aditocco2/overblinking/media/huell.gif

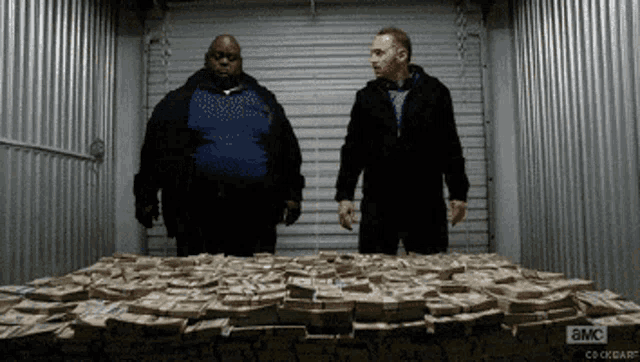
media/huell.gif
