aditocco2/overblinking/media/patriot.jpg

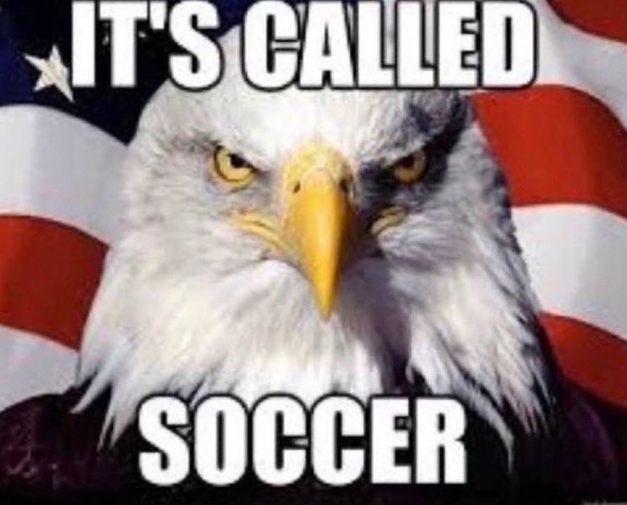
media/patriot.jpg
