aditocco2/overblinking/FreeRTOS-Kernel-main/.github/media/pr_process.png

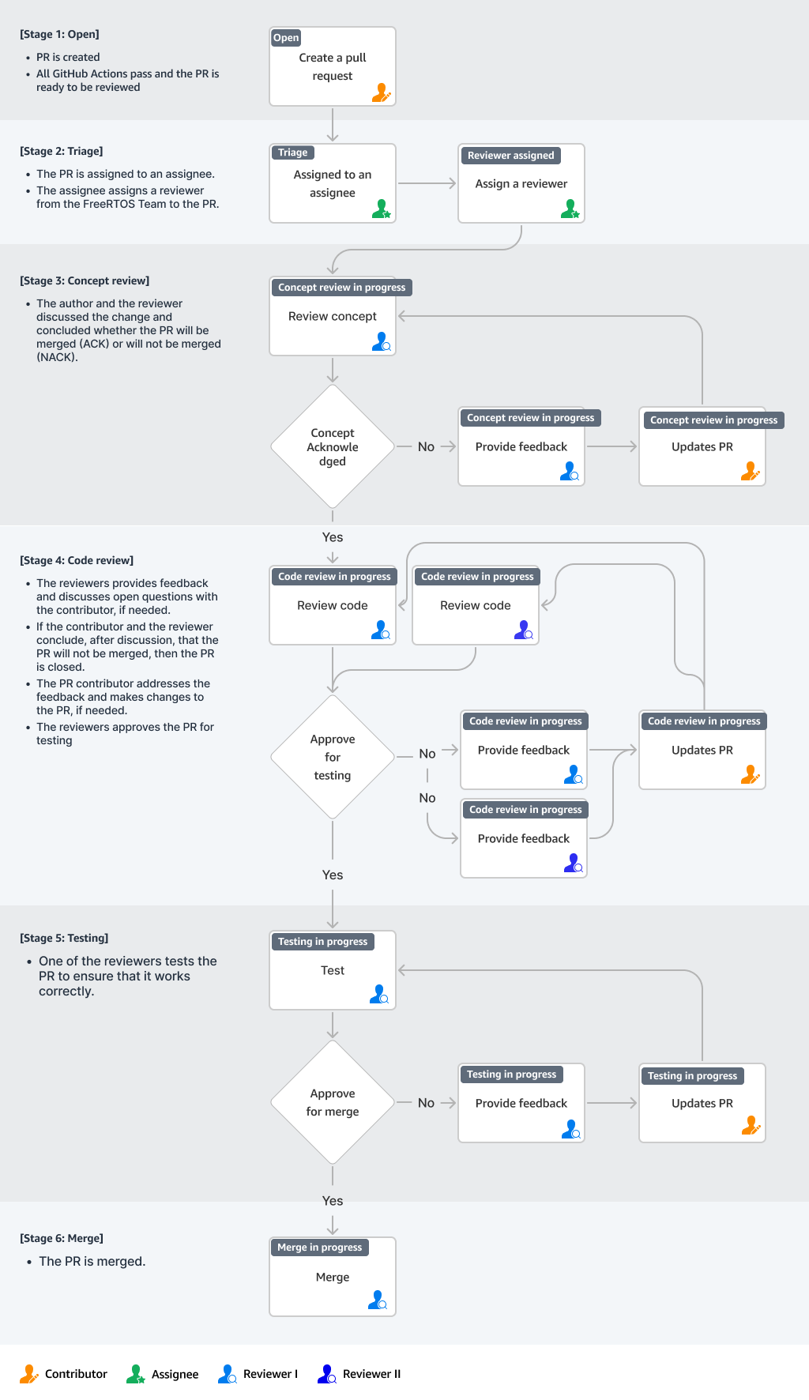
FreeRTOS-Kernel-main/.github/media/pr_process.png
