aditocco2/overblinking/media2/2Frames.gif

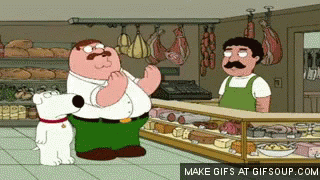
media2/2Frames.gif
