aditocco2/overblinking/media2/bird.gif

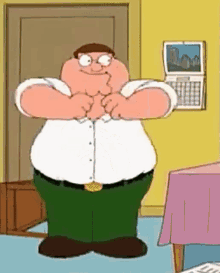
media2/bird.gif
