aditocco2/overblinking/media2/fries2.gif

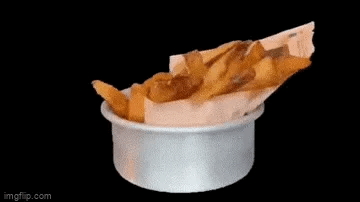
media2/fries2.gif
