aditocco2/overblinking/media2/plink.gif

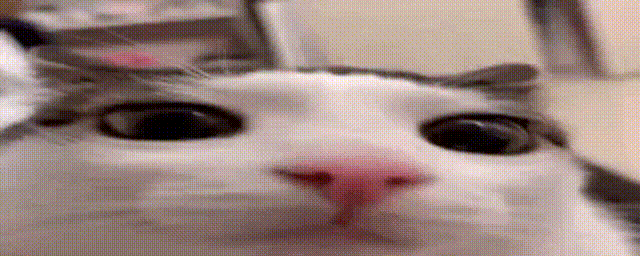
media2/plink.gif
