aditocco2/overblinking/media2/saul.gif

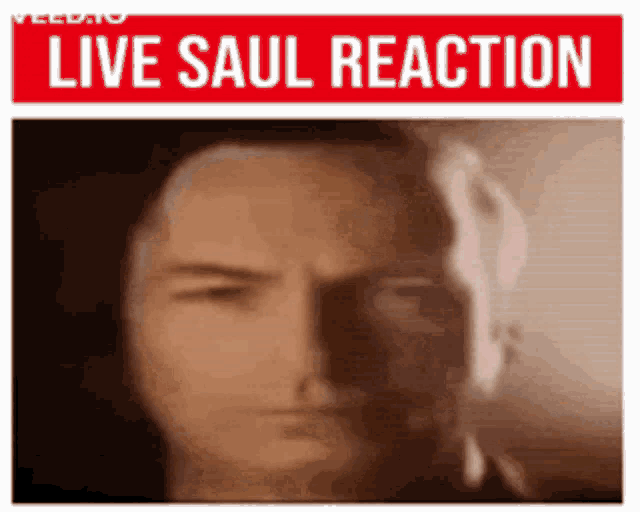
media2/saul.gif
