aditocco2/overblinking/media2/spongedance.gif

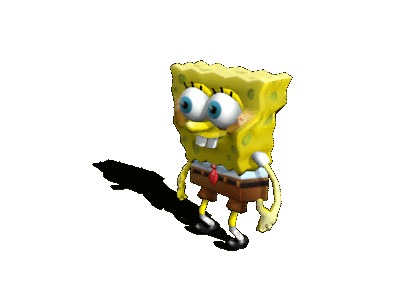
media2/spongedance.gif
