aditocco2/overblinking/media2/ugandan.gif

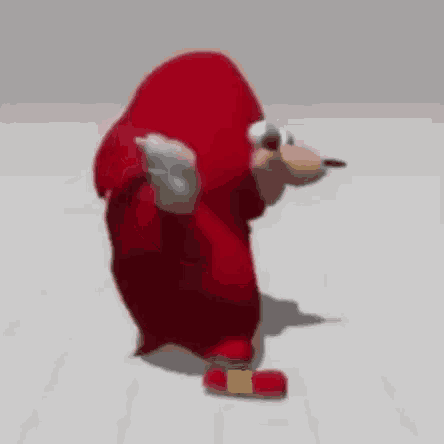
media2/ugandan.gif
