aditocco2/overblinking/media/all a man need fr.png

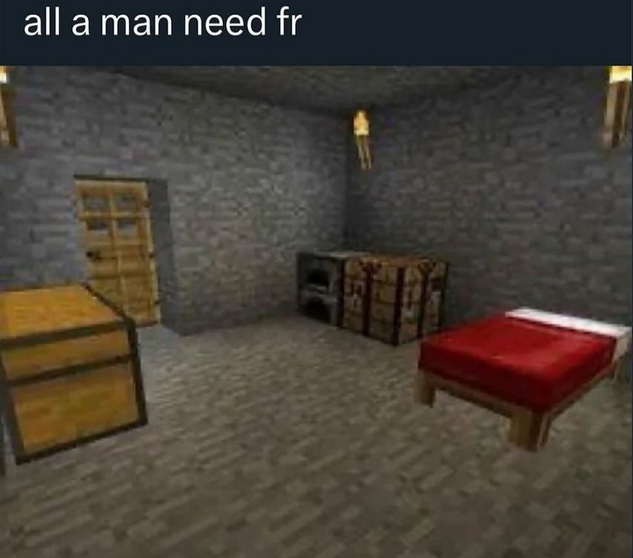
media/all a man need fr.png
