aditocco2/overblinking/media/chicken villager.jpg

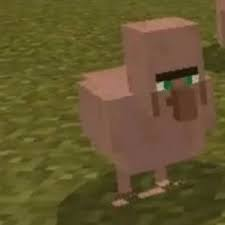
media/chicken villager.jpg
