aditocco2/overblinking/media/goog.jpg

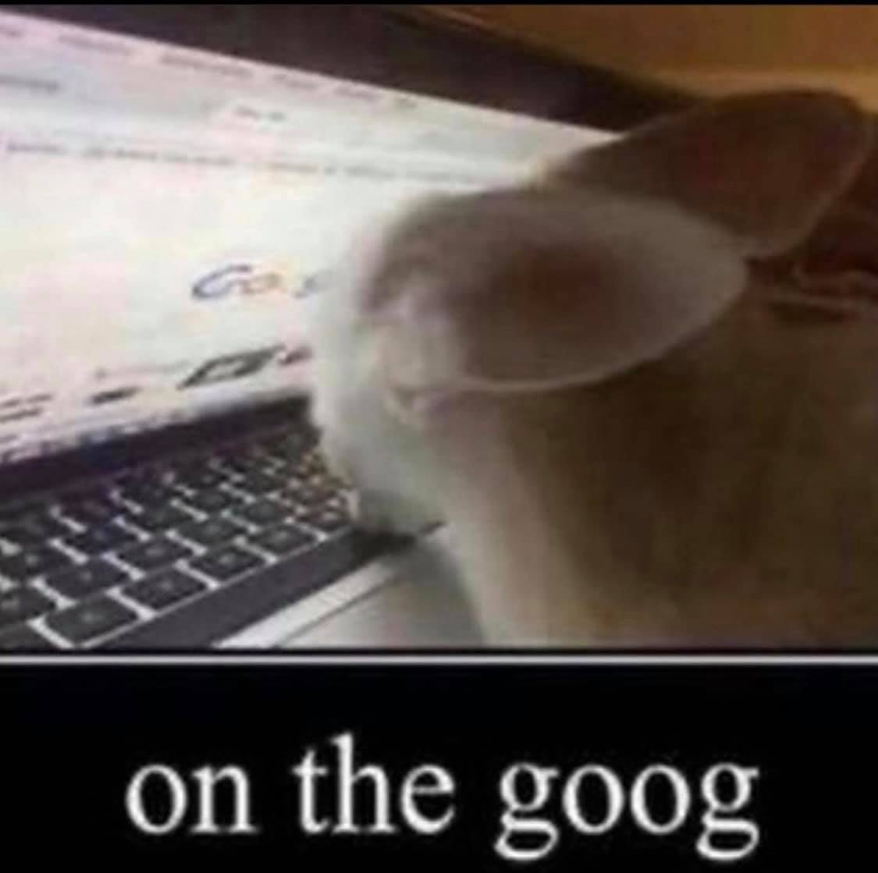
media/goog.jpg
