aditocco2/overblinking/media/ham sammich.png

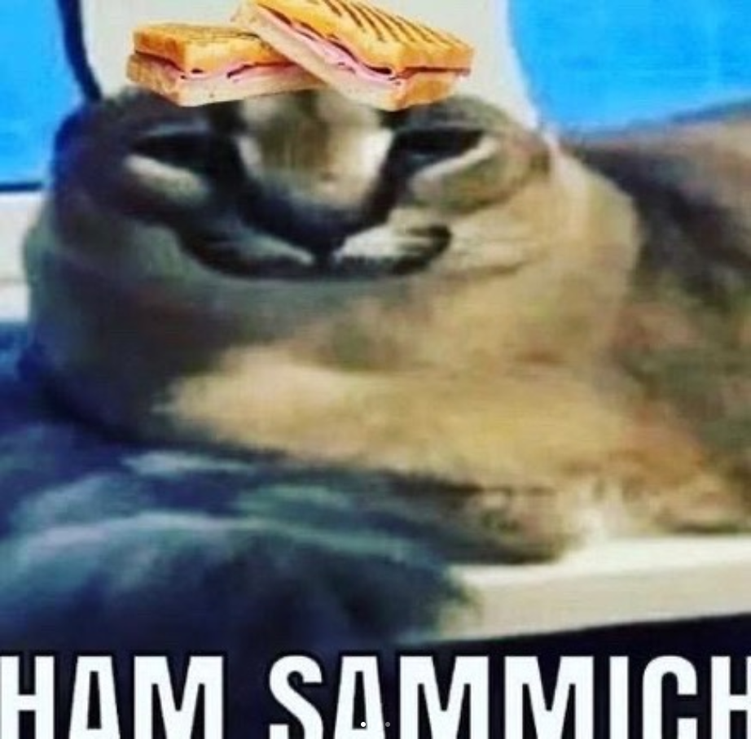
media/ham sammich.png
