aditocco2/overblinking/media/hands.jpg

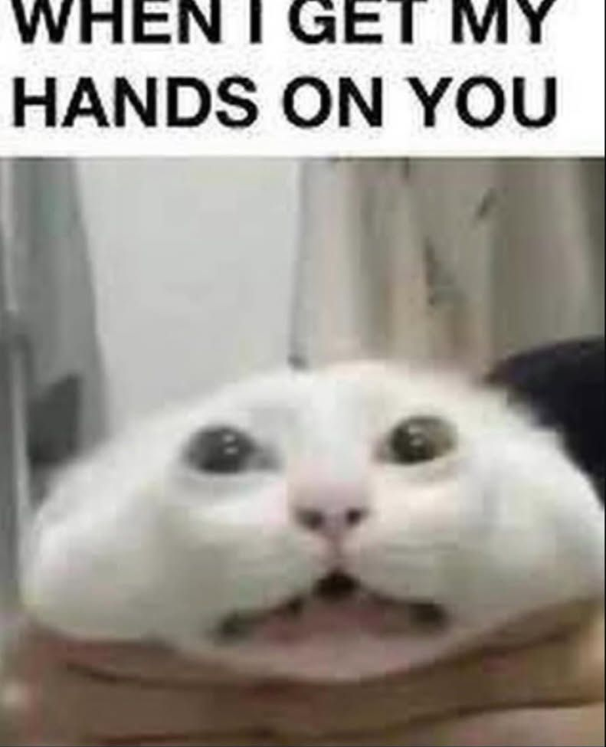
media/hands.jpg
