aditocco2/overblinking/media/holy fucking shit 2019 was 5 years ago.png

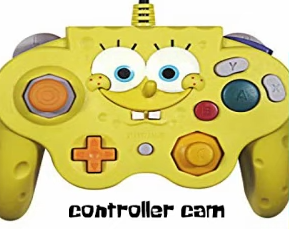
media/holy fucking shit 2019 was 5 years ago.png
