aditocco2/overblinking/media/it do not matter.jpg

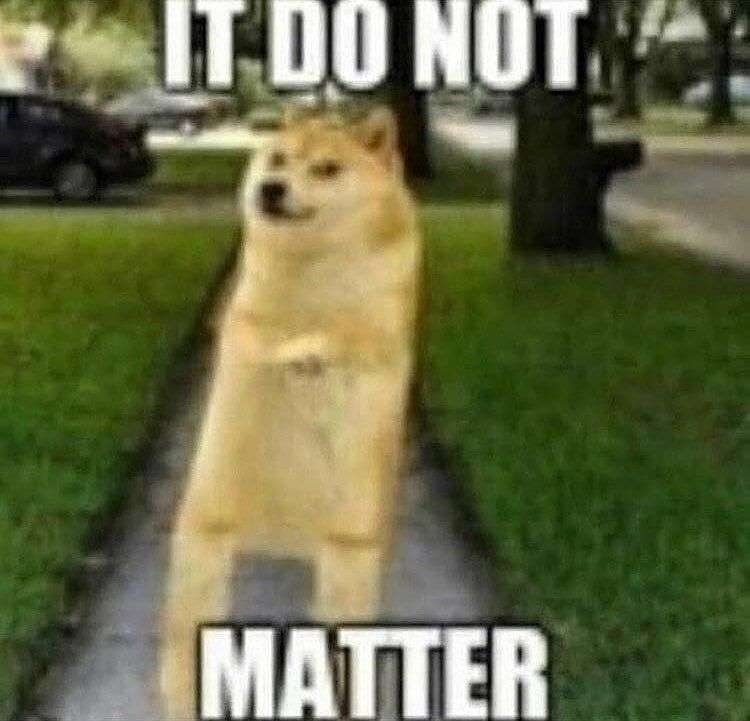
media/it do not matter.jpg
