aditocco2/overblinking/media/lagoon trigger.png

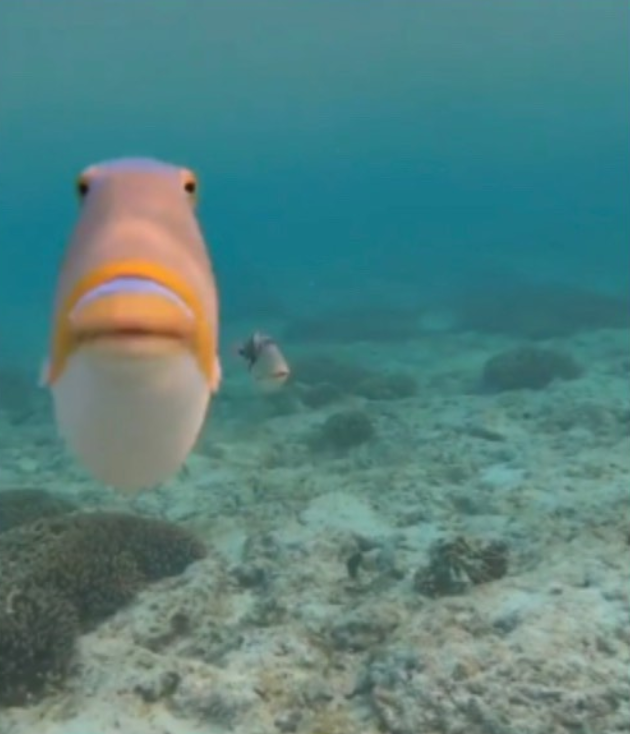
media/lagoon trigger.png
