aditocco2/overblinking/media/man.jpg

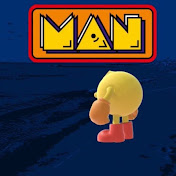
media/man.jpg
