aditocco2/overblinking/media/mug moment.png

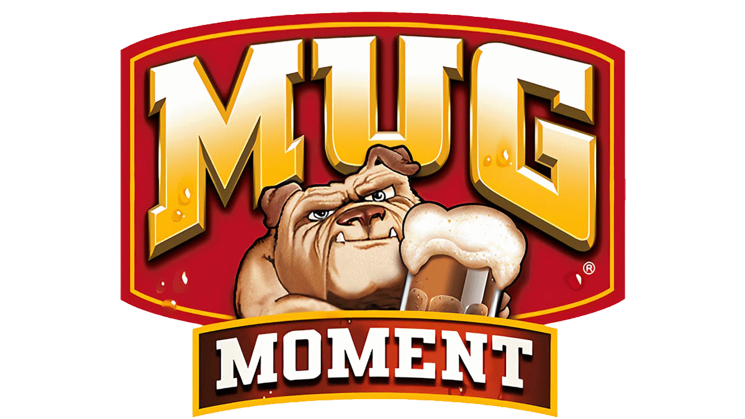
media/mug moment.png
