aditocco2/overblinking/media/normal.jpg

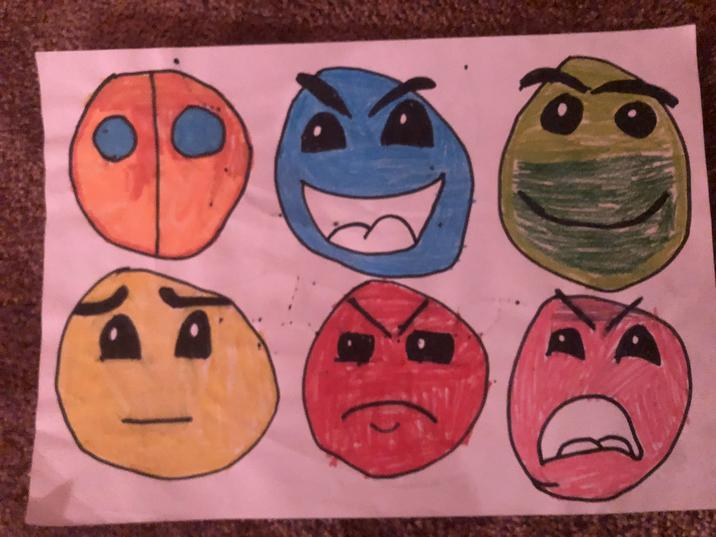
media/normal.jpg
