aditocco2/overblinking/media/numb.png

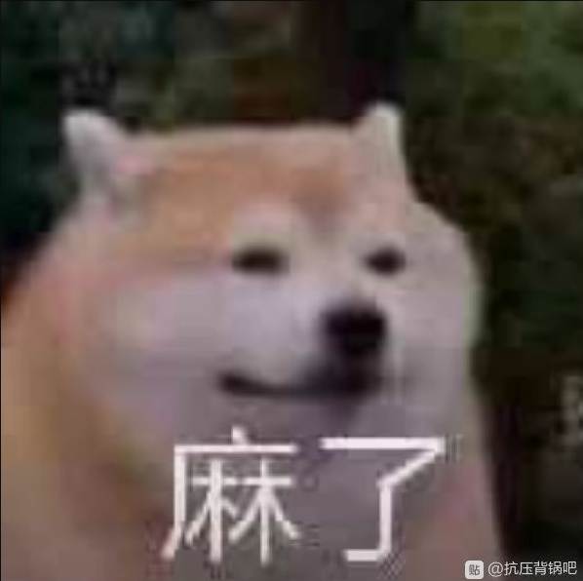
media/numb.png
