aditocco2/overblinking/media/petar.png

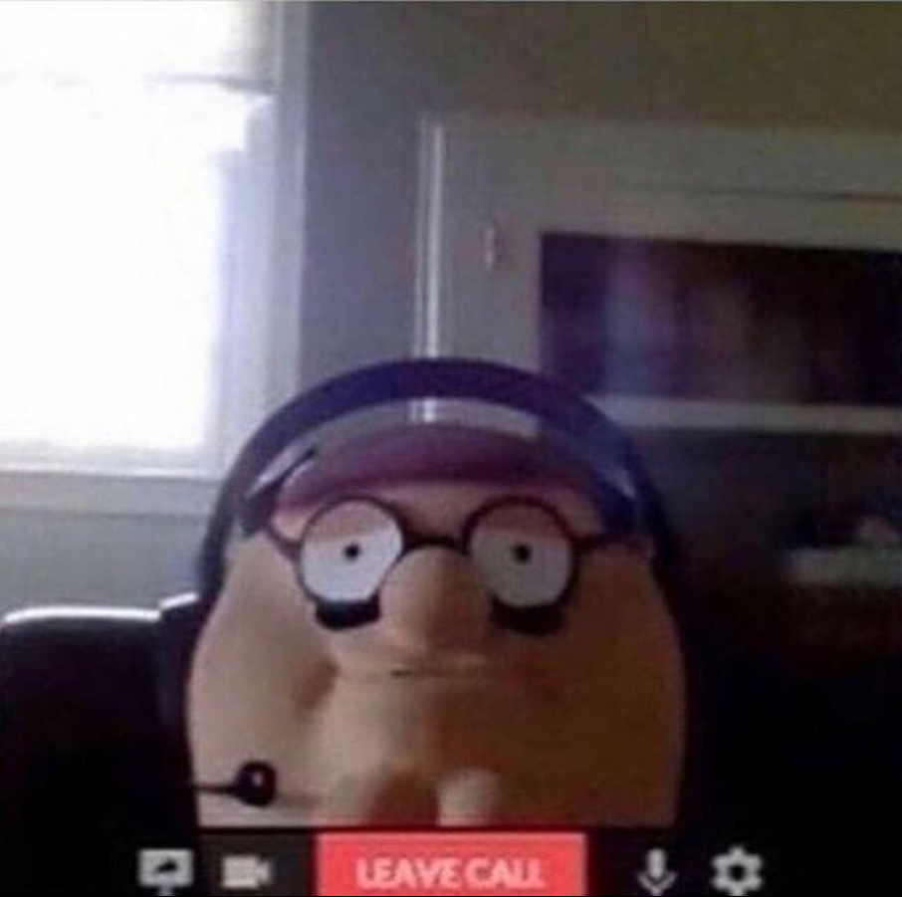
media/petar.png
