aditocco2/overblinking/media/pitbull.jpg

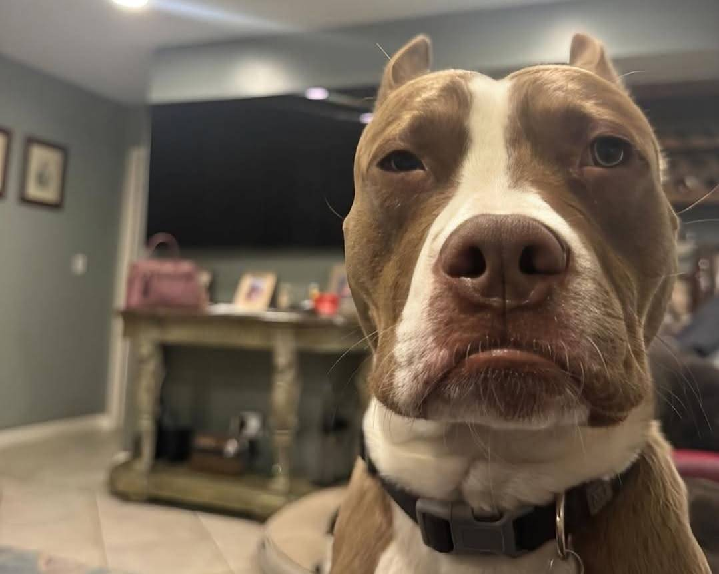
media/pitbull.jpg
