aditocco2/overblinking/media/shoe it to em.jpg

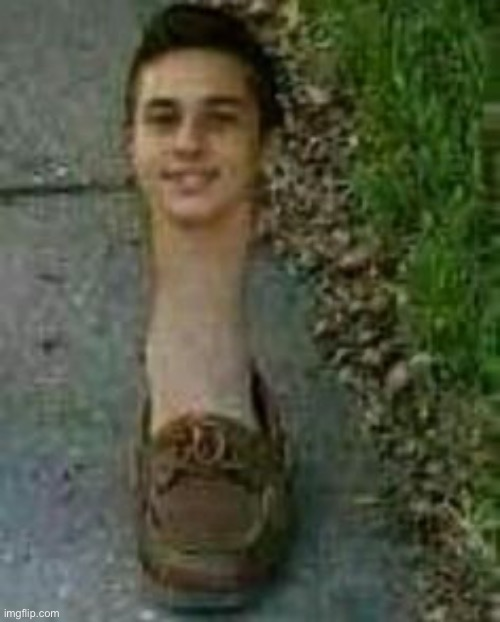
media/shoe it to em.jpg
