aditocco2/overblinking/media/WawaCalling.jpg

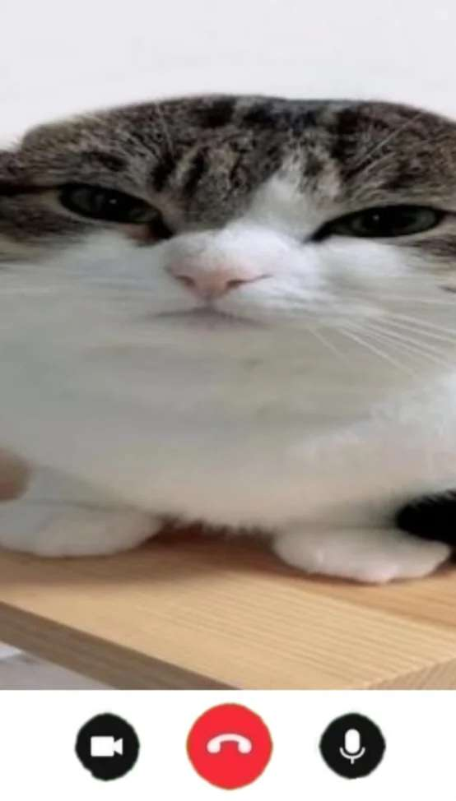
media/WawaCalling.jpg
