aditocco2/overblinking/python/media_slideshow/iuh.gif

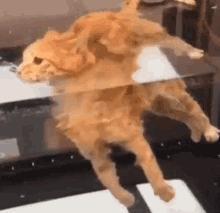
python/media_slideshow/iuh.gif
