aditocco2/overblinking/release/loader/media_slideshow/825763.jpg

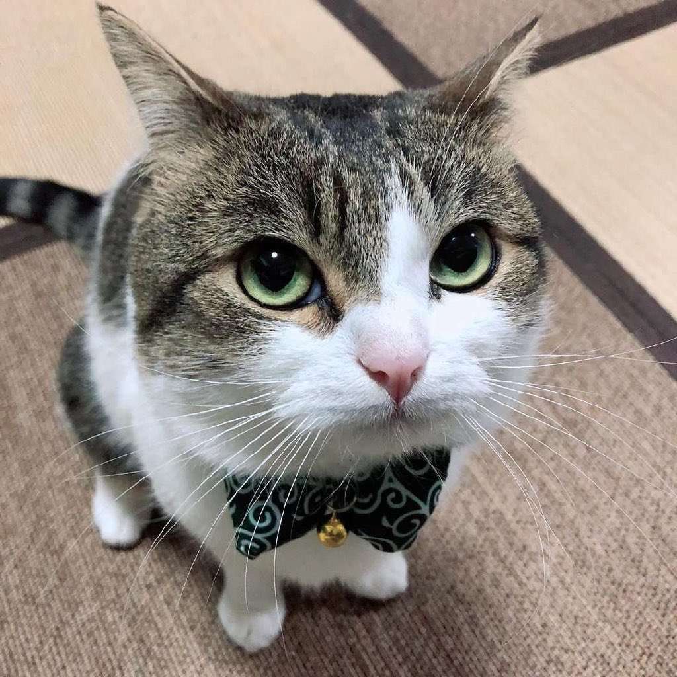
release/loader/media_slideshow/825763.jpg
